rtreichl/led_cube/avr/src/ascci.c

/*
 * ascci.c
 *
 * Created: 06.08.2014 23:45:12
 *  Author: Richi
 */ 
#include <avr/pgmspace.h>
#include <avr/io.h>
#include <include/ascii.h>

const uint8_t string[] PROGMEM = "LED-Cube";

const uint8_t font8x8[][8] PROGMEM = {

    {
        0x00,
        0x00,
        0x00,
        0x00,
        0x00,
        0x00,
        0x00,
        0x00
    },
    {		// !
        0x04,
        0x04,
        0x04,
        0x04,
        0x00,
        0x00,
        0x04,
        0x00
    },
    {		// "
        0x0A,
        0x0A,
        0x0A,
        0x00,
        0x00,
        0x00,
        0x00,
        0x00
    },
    {		// #
        0x0A,
        0x0A,
        0x1F,
        0x0A,
        0x1F,
        0x0A,
        0x0A,
        0x00
    },
    {		// $
        0x04,
        0x0F,
        0x14,
        0x0E,
        0x05,
        0x1E,
        0x04,
        0x00
    },
    {		// %
        0x18,
        0x19,
        0x02,
        0x04,
        0x08,
        0x13,
        0x03,
        0x00
    },
    {		// &
        0x0C,
        0x12,
        0x14,
        0x08,
        0x15,
        0x12,
        0x0D,
        0x00
    },
    {		// '
        0x0C,
        0x04,
        0x08,
        0x00,
        0x00,
        0x00,
        0x00,
        0x00
    },
    {		// (
        0x02,
        0x04,
        0x08,
        0x08,
        0x08,
        0x04,
        0x02,
        0x00
    },
    {		// )
        0x08,
        0x04,
        0x02,
        0x02,
        0x02,
        0x04,
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
    0x00
},
{		// 77
    0x00,
    0x00,
    0x00,
    0x00,
    0x00,
    0x00,
    0x00,
    0x00
},
{		// 78
    0x00,
    0x00,
    0x00,
    0x00,
    0x00,
    0x00,
    0x00,
    0x00
},
{		// 79
    0x00,
    0x00,
    0x00,
    0x00,
    0x00,
    0x00,
    0x00,
    0x00
},
{		// 7A
    0x00,
    0x00,
    0x00,
    0x00,
    0x00,
    0x00,
    0x00,
    0x00
},
{		// 7B
    0x00,
    0x00,
    0x00,
    0x00,
    0x00,
    0x00,
    0x00,
    0x00
},
{		// 7C
    0x00,
    0x00,
    0x00,
    0x00,
    0x00,
    0x00,
    0x00,
    0x00
},
{		// 7D
    0x00,
    0x00,
    0x00,
    0x00,
    0x00,
    0x00,
    0x00,
    0x00
},
{		// 7E
    0x00,
    0x00,
    0x00,
    0x00,
    0x00,
    0x00,
    0x00,
    0x00
},
{		// 7F
    0x00,
    0x00,
    0x00,
    0x00,
    0x00,
    0x00,
    0x00,
    0x00
}
};
